SladkayaDoza/FlipTheCat/FlipTheCat/src/apps/wifi_app.h

#pragma once

// Экран Wi-Fi: пассивные функции анализа эфира (только приём).
//   - Scanner    : список точек доступа (SSID/BSSID/RSSI/канал/шифрование)
//   - Ch Monitor : загруженность каналов 1..13 по числу сетей (столбчатый график)
//   - Sniffer    : promiscuous-режим, счётчик кадров по типам на выбранном канале
//   - Stations   : список MAC-адресов устройств в эфире (addr2) с RSSI на канале
//
// Активные/наступательные режимы (deauth, beacon-флуд, инъекция) не реализуются.
void wifiLay();
