SladkayaDoza/FlipTheCat/FlipTheCat/src/hal/button.h

#pragma once
#include <EncButton.h>

extern VirtButton up;
extern VirtButton down;
extern VirtButton left;
extern VirtButton right;
extern VirtButton ok;
extern VirtButton back;
extern VirtButton top_left;
extern VirtButton top_right;
